adwaithas-2004/Q-Flo-Prototype/hardware/kicad/PetrolQuality.kicad_sch

## KiCad design hardware/kicad/PetrolQuality.kicad_sch (2026-09-29)

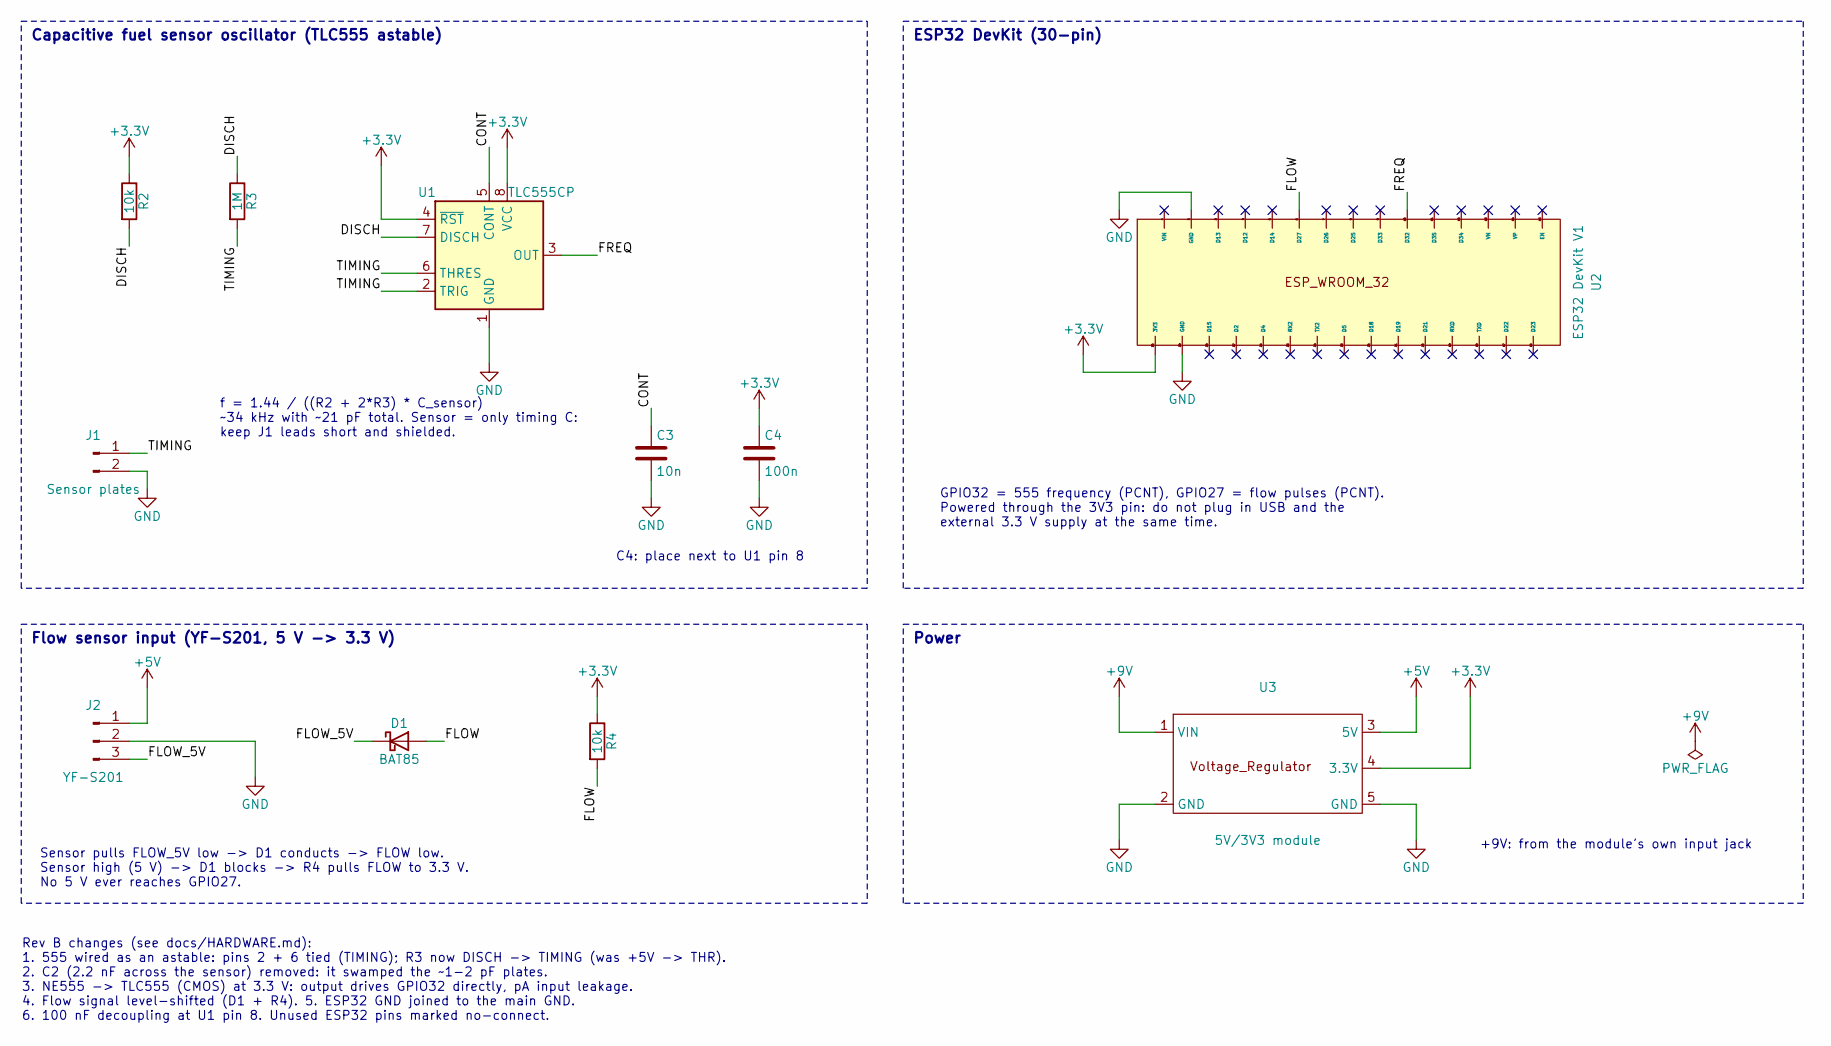
[picture p2: schematic PetrolQuality.kicad_sch]

Parts:
C3: 10n; CP_Radial_D5.0mm_P2.50mm
C4: 100n; C_Disc_D5.0mm_W2.5mm_P5.00mm
D1: BAT85; D_DO-35_SOD27_P7.62mm_Horizontal
J1: Sensor plates; JST_PH_B2B-PH-K_1x02_P2.00mm_Vertical
J2: YF-S201; JST_PH_B3B-PH-K_1x03_P2.00mm_Vertical
R2, R4: 10k; R_Axial_DIN0207_L6.3mm_D2.5mm_P7.62mm_Horizontal
R3: 1M; R_Axial_DIN0207_L6.3mm_D2.5mm_P7.62mm_Horizontal
U1: TLC555CP; DIP-8_W7.62mm
U2: ESP32 DevKit V1; ESP_32
U3: 5V/3V3 module; Voltage_Regulator

Connections:
+3.3V: C4.1, R2.1, R4.1, U1.4 (~RST), U1.8 (VCC), U2.30 (3V3), U3.4 (3.3V)
+5V: J2.1, U3.3 (5V)
+9V: U3.1 (VIN)
CONT: C3.1, U1.5 (CONT)
DISCH: R2.2, R3.1, U1.7 (DISCH)
FLOW: D1.2 (A), R4.2, U2.6 (D27)
FLOW_5V: D1.1 (K), J2.3
FREQ: U1.3 (OUT), U2.10 (D32)
GND: C3.2, C4.2, J1.2, J2.2, U1.1 (GND), U2.2 (GND), U2.29 (GND), U3.2 (GND), U3.5 (GND)
TIMING: J1.1, R3.2, U1.2 (TRIG), U1.6 (THRES)

Notes on the sheet:
Capacitive fuel sensor oscillator (TLC555 astable)
f = 1.44 / ((R2 + 2*R3) * C_sensor) ~34 kHz with ~21 pF total. Sensor = only timing C: keep J1 leads short and shielded.
C4: place next to U1 pin 8
Flow sensor input (YF-S201, 5 V -> 3.3 V)
Sensor pulls FLOW_5V low -> D1 conducts -> FLOW low. Sensor high (5 V) -> D1 blocks -> R4 pulls FLOW to 3.3 V. No 5 V ever reaches GPIO27.
ESP32 DevKit (30-pin)
GPIO32 = 555 frequency (PCNT), GPIO27 = flow pulses (PCNT). Powered through the 3V3 pin: do not plug in USB and the external 3.3 V supply at the same time.
Power
+9V: from the module's own input jack
Rev B changes (see docs/HARDWARE.md): 1. 555 wired as an astable: pins 2 + 6 tied (TIMING); R3 now DISCH -> TIMING (was +5V -> THR). 2. C2 (2.2 nF across the sensor) removed: it swamped the ~1-2 pF plates. 3. NE555 -> TLC555 (CMOS) at 3.3 V: output drives GPIO32 directly, pA input leakage. 4. Flow 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
